Foundation-Devices/passport-electronics/Battery Board/Assembly/North Board Assembly/Bill of Materials - XLS/BOM_FD-JL-PCB-BB_C2.PDF

Line # | Fitted | Rev | Name | Description | Quantity | Designator | Manufacturer 1 | Manufacturer Part Number 1
1 | Fitted | C2 | FD-JL-PCB-BB | PCB - Juliet - Battery Board | 1 PCB1
2 | Fitted | | SMTSO-080-4ET | Surface Mount Nut | 1 N1 | | PennEngineering | SMTSO-080-4ET
3 | Fitted | | RES 0OHM JUMPER 1/8W 0805 | 0Ohms Jumper 0.125W, 1/8W Chip Resistor 0805 (2012 Metric) | 1 R1 | | Vishay | CRCW08050000Z0EA
4 | Fitted | | 0393-0-00-15-00-00-09-0* | Pin Receptacle Connector 0.065" ~ 0.082" (1.65mm ~ 2.08mm) No Tail Solder | 1 P2 | | Mill-Max | 0393-0-00-15-00-00-09-0*
5 | Fitted | | 0871-0-57-20-82-14-11-0 | Contact Spring Surface Mount | 1 P3 | | Mill-Max | 0871-0-57-20-82-14-110
6 | Not Fitted | | 829-22-002-20-002101 | 2 Position Spring Piston Connector Through Hole, Right Angle | 0 P1 | | Mill-Max | 829-22-002-20-002101
