Foundation-Devices/passport-electronics/Battery Board/Assembly/North Board Assembly/Assembly Drawings/ASSY_FD-JL-PCB-BB_C2.PDF

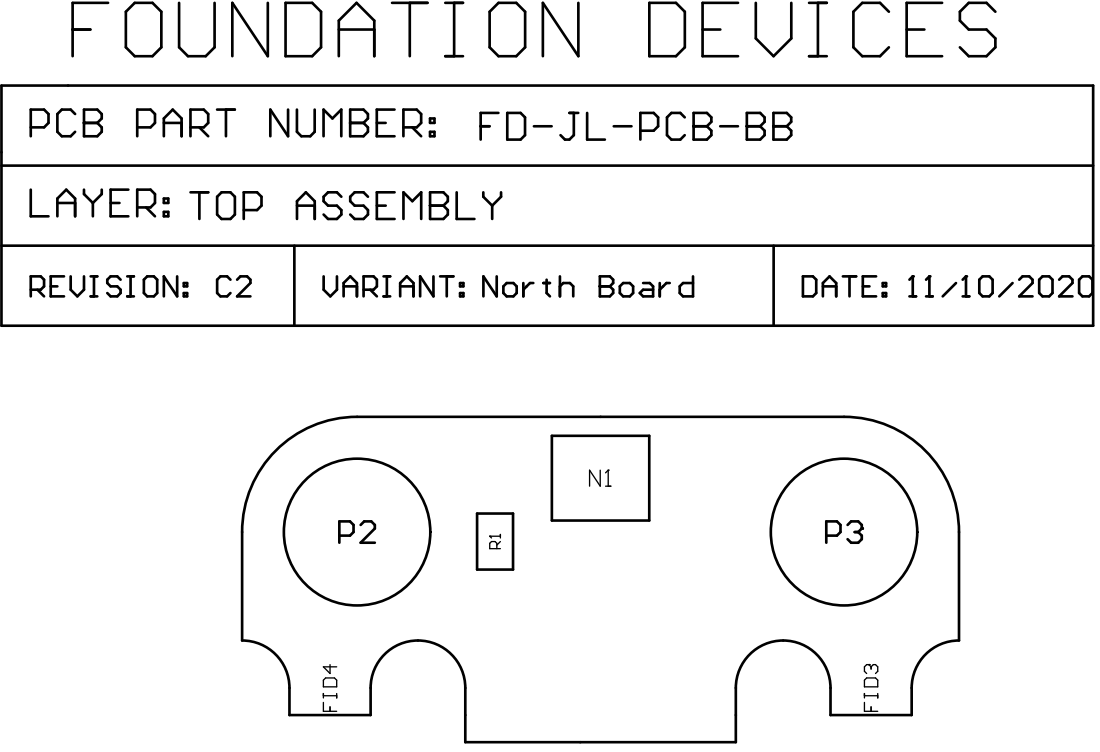
[picture p47: page 1]

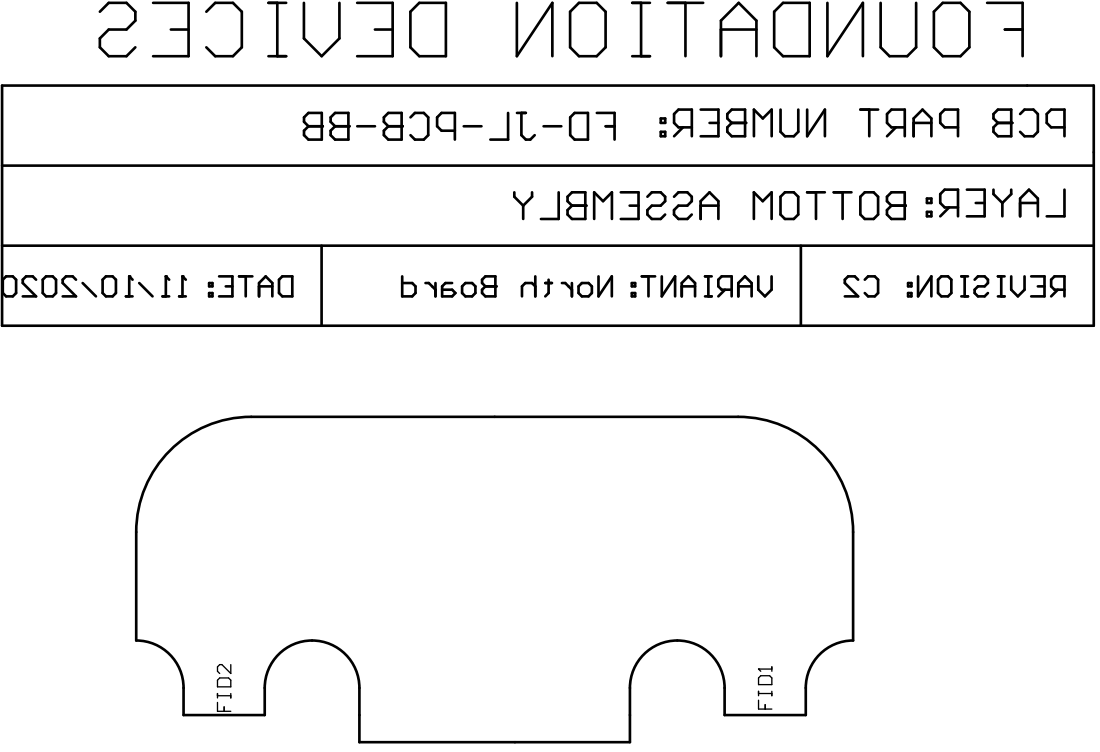
[picture p48: page 2]
