Foundation-Devices/passport-electronics/Battery Board/Assembly/South Board Assembly/Assembly Drawings/ASSY_FD-JL-PCB-BB_C2.PDF

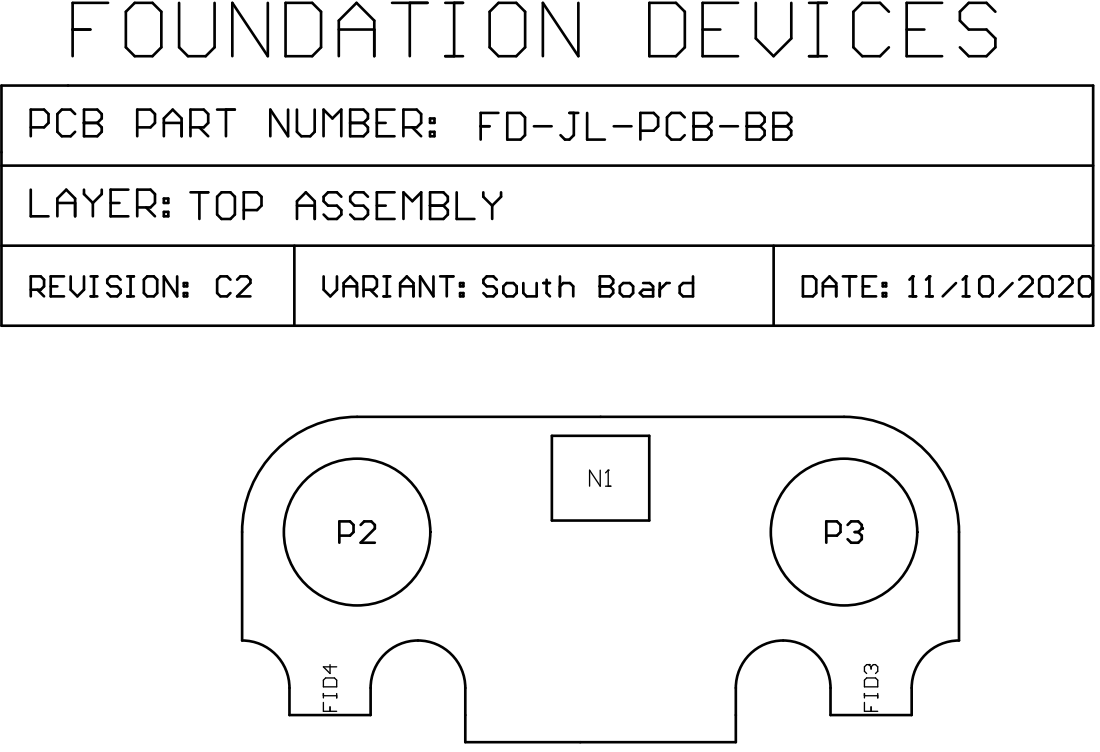
[picture p49: page 1]

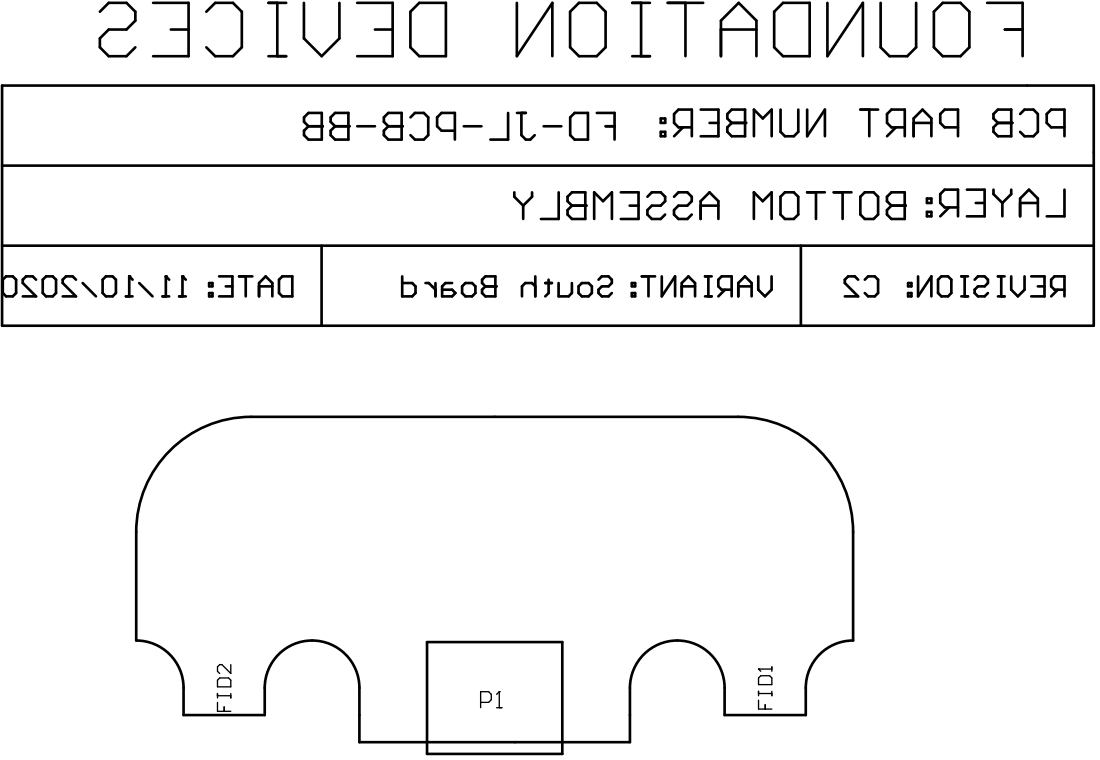
[picture p50: page 2]
